DEFOR111/KLIK-/BOM/ali cart full price (2).png

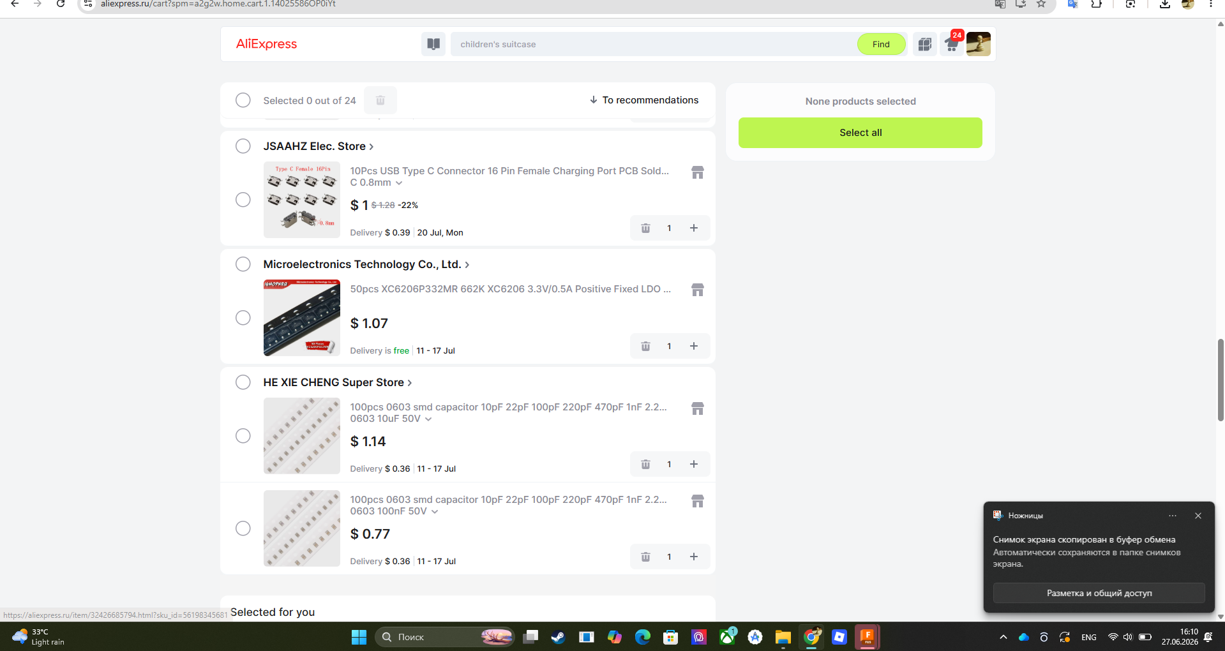
BOM/ali cart full price (2).png
