DEFOR111/KLIK-/BOM/JLCBPCB cart.png

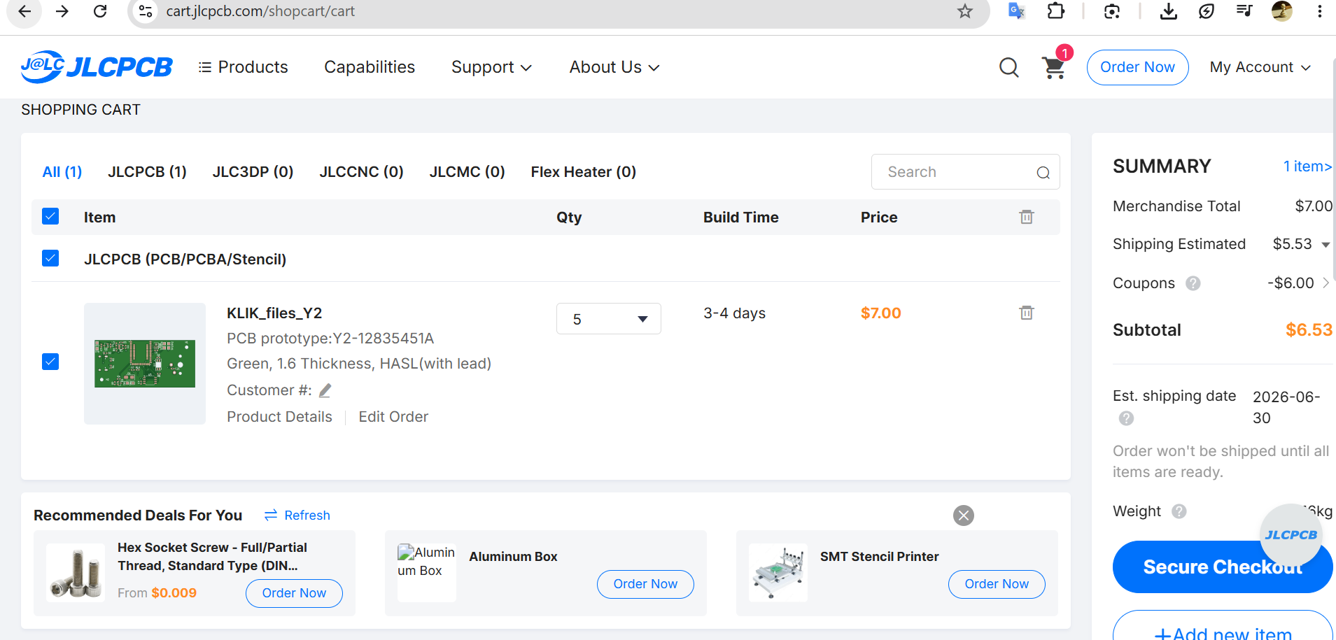
BOM/JLCBPCB cart.png
